masterkrieger/BarrKeeb16/Images/BarrKeeb16_1.jpg

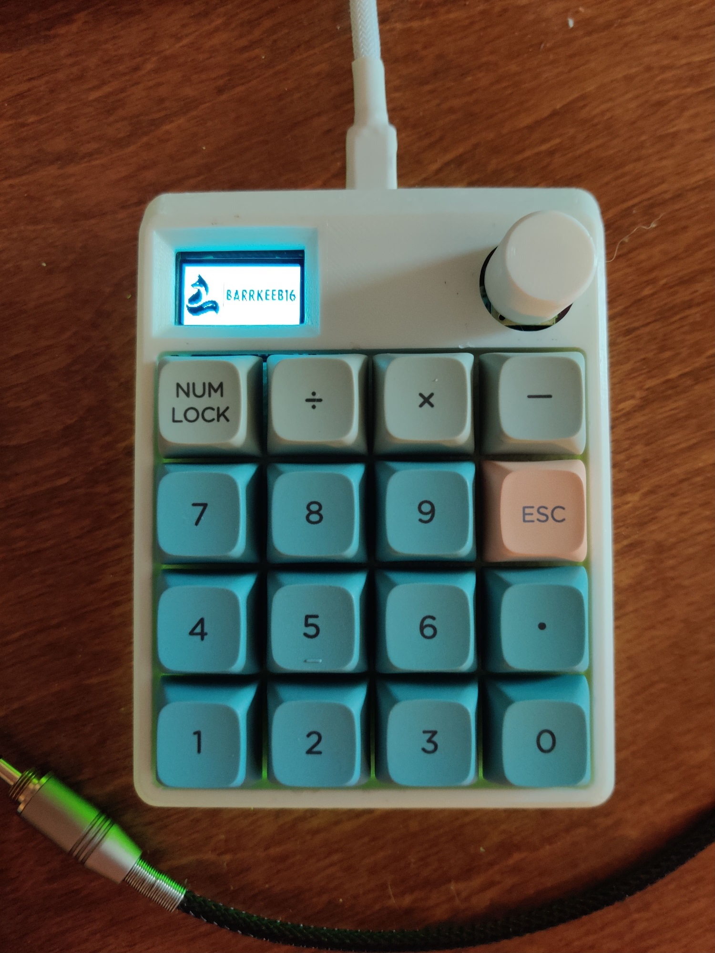
Images/BarrKeeb16_1.jpg
